alinxalinx/AXU4EV-P_AXU5EV-P/linux/.images_for_documents/5.png

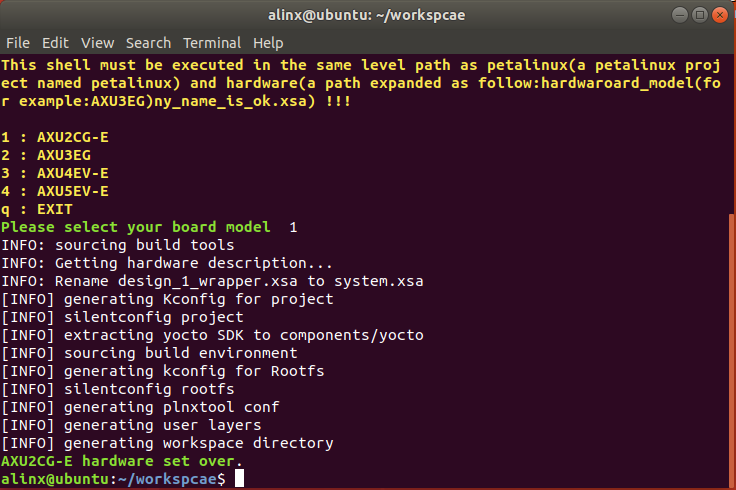
linux/.images_for_documents/5.png
