alinxalinx/AXU4EV-P_AXU5EV-P/linux/.images_for_documents/8.png

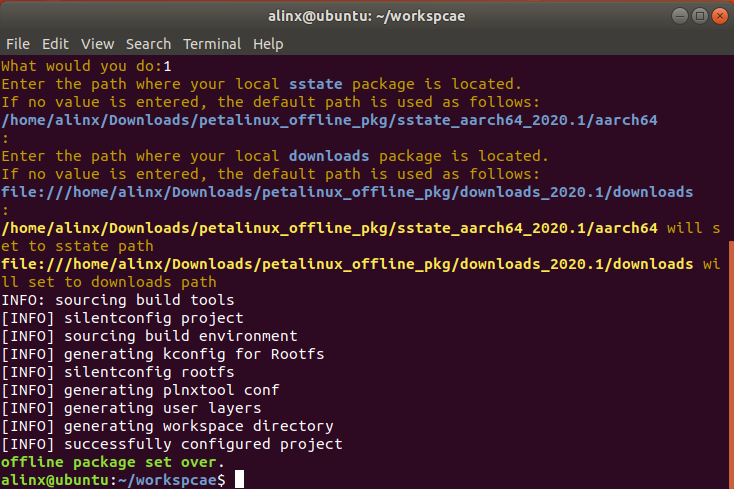
linux/.images_for_documents/8.png
