alinxalinx/AXU4EV-P_AXU5EV-P/linux/.images_for_documents/15.png

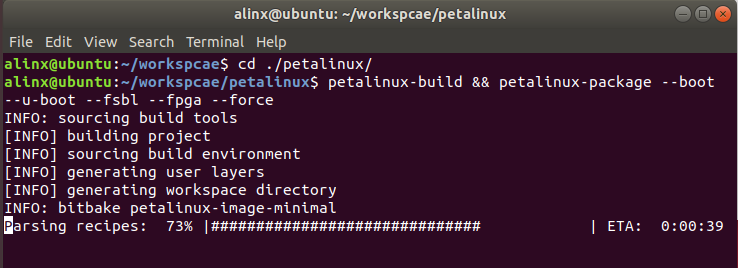
linux/.images_for_documents/15.png
