alinxalinx/AXU4EV-P_AXU5EV-P/vivado/auto_create_project/src/constraints/rs485.xdc

set_property PACKAGE_PIN A10 [get_ports {RS485_0_DE_tri_o[0]}]
set_property IOSTANDARD LVCMOS33 [get_ports {RS485_0_DE_tri_o[0]}]

set_property PACKAGE_PIN AH10 [get_ports {RS485_0_rxd}]
set_property IOSTANDARD LVCMOS33 [get_ports {RS485_0_rxd}]

set_property PACKAGE_PIN AG10 [get_ports {RS485_0_txd}]
set_property IOSTANDARD LVCMOS33 [get_ports {RS485_0_txd}]

set_property PACKAGE_PIN B11 [get_ports {RS485_1_DE_tri_o[0]}]
set_property IOSTANDARD LVCMOS33 [get_ports {RS485_1_DE_tri_o[0]}]

set_property PACKAGE_PIN AH12 [get_ports {RS485_1_rxd}]
set_property IOSTANDARD LVCMOS33 [get_ports {RS485_1_rxd}]

set_property PACKAGE_PIN AH11 [get_ports {RS485_1_txd}]
set_property IOSTANDARD LVCMOS33 [get_ports {RS485_1_txd}]
