alinxalinx/AXU4EV-P_AXU5EV-P/vivado/auto_create_project/src/constraints/gpio.xdc

set_property PACKAGE_PIN AE14 [get_ports {btns_tri_i[0]}]
set_property IOSTANDARD LVCMOS33 [get_ports {btns_tri_i[0]}]

set_property PACKAGE_PIN AE15 [get_ports {leds_tri_o[0]}]
set_property IOSTANDARD LVCMOS33 [get_ports {leds_tri_o[0]}]
