alinxalinx/AXU4EV-P_AXU5EV-P/vivado/auto_create_project/src/constraints/uart.xdc

set_property PACKAGE_PIN AA10 [get_ports {uart_rxd}]
set_property IOSTANDARD LVCMOS33 [get_ports {uart_rxd}]

set_property PACKAGE_PIN AA11 [get_ports {uart_txd}]
set_property IOSTANDARD LVCMOS33 [get_ports {uart_txd}]
